mend0z0/Blender/Hardware/_Sub_HW_Blender/v1_20230918/Released Folder/v1.0 - 20230918/README.md

### This readme file explains the folder structure of this released version.

#### 1. Board Assembly: Any document that is related to assembly will be in this folder

	1. Assembly Guide:
		1. _MASM_Prj_vXY.html	--> This is for hand assembly
		2. _AASM_Prj_vXY.???	--> This is for machine assembly

	2. Board Statistics:
		1. _STATISTICS_Prj_vXY.txt

	3. BOM:
		1. _BOM_Prj_vXY.csv

	4. Netlist:
		1. _NETLIST_Prj_vXY.net

	5. Pick And Place:
		1. _PNP_Prj_vXY.csv

#### 2. Media Content: Any document that is related to assembly will be in this folder
	
	1. Picutre
		1. _3DView_Prj_vXY.png
		2. _3DView_Bottom_Prj_vXY.png
		3. _3DView_Top_Prj_vXY.png
		4. _CADView_Prj_vXY.png

	2. Video
		1. _Video_Prj_vXY_Title.mp4

#### 3. PCB Manufacturing: Any document that is related to manufacturing the board will be in this folder

	1. CNC Drill:
		_DRL_Prj_vXY.drl		
		_DRL_MAP_Prj_vXY.gbr

	2. Gerber:
		1. _GBR_Top_SilkScreen_Prj_vXY.gto
		2. _GBR_Top_Mask_Prj_vXY.gts
		3. _GBR_Top_Cu_Prj_vXY.gtl
		4. _GBR_In1_Cu_Prj_vXY.g2
		5. _GBR_In2_Cu_Prj_vXY.g3
		6. _GBR_In3_Cu_Prj_vXY.g4
		7. _GBR_In4_Cu_Prj_vXY.g5
		8. _GBR_Bottom_Cu_Prj_vXY.gbl
		9. _GBR_Bottom_Mask_Prj_vXY.gbs
		10. _GBR_Bottom_SilkScreen_Prj_vXY.gbo
		11. _GBR_EdgeCut_Prj_vXY.gml

	3. Stackup Information:
		_STACKUP_Prj_vXY.csv

	4. Stencil:
		_STC_Top_Prj_vXY.gtp
		_STC_Bottom_Prj_vXY.gbp
		_STC_EdgeCut_Prj_vXY.gml

#### 4. Schematic (PDF): Placing the PDF version of the schematic captures

#### 5. Source files: All the sources except the history files.

#### 6. STEP: The 3D Model file of the project will be in this folder.
	1. _STEP_Prj_vXY.stp
