mend0z0/Blender/Firmware/v1_20231222/Design Folder/_FW_Blender/Drivers/Peripherals/_drv_peripherals.h

/****************************************************************************************************
*
*   Project Name:       Blender
*   @Brief Description: Blending audio spec with light spectrum
*   File Status:	    DRAFT   (DRAFT , PRELIMINARY, CHECKED, RELEASED)
*
*	File Name:	xxxx.h
*	Version:	01
*	Revision:	01
*	Date:		2023/01/dd
*	License:	Open-source
*	******************************** Project Description *******************************************
*	@Detailed Description: The Blender project's purpose is to extract digitalized sound characteristics
*   like amplitude and frequency, which are transferring through the S/PDIF protocol, and display the amplitude
*   of different frequencies by the dominant color of the input VGA received signal. So the base color will be
*   determined by VGA input, and a spectrum of that color will be displayed over/on the DMX/WS2812 chip. Also,
*   the specification of the sound will be displayed on an OLED, and the sound will be played by a chip that has
*   an integrated DAC in it. The data to DAC will be transferred via the I2S protocol.
*
*	******************************** File Description *******************************************
*	@Detailed Description:
*
*
*
*	*********************************  Hardware Info  **********************************************
*   Name:       _HW_Blender
*   Version:    v1.0
*	*********************************  Processor Info **********************************************
*	Processor:          STM32F446RCT6 32-Bits
*	Clock Frequency:    180.000	MHz
*	RAM/SRAM Size:      128.00	KBytes
*	Flash Size:         256.00	KBytes
*	***********************************  Case Style  ***********************************************
*	Local Variables = camelCase			Global Variables = g_camelCase
*	Headers = SCREAMIN_SNAKE_CASE
*   Macros = SCREAMING_SNAKE_CASE
*   Const Variables = SCREAMING_SNAKE_CASE
*	Functions = PascalCase				Initialize Functions = _lower_case
*	Struct = lower_case					Struct.members = camelCase
*	Enum = lower_case					Enum Members = SNAKE_CASE
*	Pointer Variables = p_camelCase
*	*********************************** Contact Info ***********************************************
*	Author: Siavash Taher Parvar
*	Github: www.github.com/Mend0z0
****************************************************************************************************/
#ifndef _DRV_PERIPHERALS_H_
#define _DRV_PERIPHERALS_H_
/****************************************************************************************************
****************************       HEADERS DECLARATION       ****************************************
*****************************************************************************************************/
#include "main.h"

/****************************************************************************************************
****************************        MACRO DECLARATION         ***************************************
*****************************************************************************************************/

/****************************************************************************************************
****************************   DEFINED VARIABLES DECLARATION    *************************************
*****************************************************************************************************/
#define	PAM8003_DEFAULT_VALUE_PIN_SHDN  0U
#define PAM8003_DEFAULT_VALUE_PIN_VOL	0U

#define PCM1754_DEFAULT_VALUE_PIN_DMP	0U 		// (1 -> DMP ON, 0 -> DMP OFF)
#define PCM1754_DEFAULT_VALUE_PIN_FMT	1U		// (1 -> 16-bit right-justified, 0 -> 24-bit I2S format)
#define PCM1754_DEFAULT_VALUE_PIN_MUTE	1U		// (1 -> MUTE ON, 0 -> MUTE OFF)

#define SSD1306_DEFAULT_VALUE_PIN_RES	0U		//
#define SSD1306_DEFAULT_VALUE_PIN_DC	0U		//
#define PWR_EN_DEFAULT_VALUE_PIN		0U		//
#define LED_IND_DEFAULT_VALUE_PIN 		0U		//

#define	DMA2_SPI1_TX_EN					1U		//
#define	DMA1_FMPI2C1_TX_EN				2U		//
#define	DMA2_UART1_TX_EN				3U		//

#define	DMA2_SPI1_TX_DIS				4U		//
#define	DMA1_FMPI2C1_TX_DIS				5U		//
#define	DMA2_UART1_TX_DIS				6U		//

#define FMPI2C_ERROR_NACK				-2		//
#define	FMPI2C_ERROR_UNKNOWN			-3		//



/****************************************************************************************************
**************************     GLOBAL FUNCTIONS DECLARATION      ************************************
*****************************************************************************************************/

/****************************************************************************************************
*   @Brief Description:	This functions holds all the functions that will initialize all the peripherals registers.
*   Function Status: 	PRILIMINARY   (DRAFT , PRILIMINARY, CHECKED, RELEASED)
*
*	************************************************************************************************
*	Function Name:			_init_Peripherals()
*	Function Scope:			Global
*	Function Parameters:	void
*	Function Return Type:	void
*	************************************************************************************************/
void _init_Peripherals( void );

/*			Digital-to-analog converter							*/

/****************************************************************************************************
*   @Brief Description:	Updating the DAC output value based on percents not real output voltage.
*   Function Status: 	PRILIMINARY   (DRAFT , PRILIMINARY, CHECKED, RELEASED)
*
*	************************************************************************************************
*	Function Name:			DACUpdate()
*	Function Scope:			Global
*	Function Parameters:	uint8_t dacValue (It's a percent from 0% to 100%)
*	Function Return Type:	void
*	************************************************************************************************/
void DACUpdate( uint8_t dacValue);

/*			General-purpose timers (TIM3)						*/

/****************************************************************************************************
*   @Brief Description:	Preset the TIM3 counter register and enabling the timer
*   Function Status: 	PRILIMINARY   (DRAFT , PRILIMINARY, CHECKED, RELEASED)
*
*	************************************************************************************************
*	Function Name:			TIM3Enable()
*	Function Scope:			Global
*	Function Parameters:	void
*	Function Return Type:	void
*	************************************************************************************************/
void TIM3Enable( void );

/****************************************************************************************************
*   @Brief Description: Disable Timer3
*   Function Status: 	PRILIMINARY   (DRAFT , PRILIMINARY, CHECKED, RELEASED)
*
*	************************************************************************************************
*	Function Name:			TIM3Disable()
*	Function Scope:			Global
*	Function Parameters:	void
*	Function Return Type:	void
*	************************************************************************************************/
void TIM3Disable( void );

/****************************************************************************************************
*   @Brief Description:	Update CCR3 register of Timer 3
*   Function Status: 	PRILIMINARY   (DRAFT , PRILIMINARY, CHECKED, RELEASED)
*
*	************************************************************************************************
*	Function Name:			TIM3UpdateCCR3()
*	Function Scope:			Global
*	Function Parameters:	uint32_t ccrValue
*	Function Return Type:	void
*	************************************************************************************************/
bool TIM3UpdateCCR3( void );

/*			Inter-integrated circuit (I2C) interface			*/

/****************************************************************************************************
*   @Brief Description:	Sending an array of data over FMPI2C1
*   Function Status: 	PRILIMINARY   (DRAFT , PRILIMINARY, CHECKED, RELEASED)
*
*	************************************************************************************************
*	Function Name:			FMPI2C1DataTx()
*	Function Scope:			Global
*	Function Parameters:	uint8_t slaveAddr, uint8_t *data, uint32_t buffSize
*	Function Return Type:	int32_t
*	************************************************************************************************/
int32_t FMPI2C1DataTx( uint8_t slaveAddr, uint8_t *data, uint32_t buffSize);

/*			Universal asynchronous receiver transmitter			*/

/****************************************************************************************************
*   @Brief Description: Sending out an array of data over UART
*   Function Status: 	PRILIMINARY   (DRAFT , PRILIMINARY, CHECKED, RELEASED)
*
*	************************************************************************************************
*	Function Name:			UART1DataTx()
*	Function Scope:			Global
*	Function Parameters:	uint8_t *data, uint32_t buffSize
*	Function Return Type:	int32_t
*	************************************************************************************************/
int32_t UART1DataTx( uint8_t *data, uint32_t buffSize);

/*			Inter-IC sound										*/
int8_t I2SDataTx( uint32_t *data);



#endif /* _DRV_PERIPHERALS_H_  */

/****************************************************************************************************
*	Revision History (Description (author, date: yyyy/mm/dd))
*
****************************************************************************************************/

/************************************     END OF THE FILE      *************************************/
