mend0z0/Blender/Firmware/v1_20231222/Design Folder/_FW_Blender/Core/Src/ISR.c

/****************************************************************************************************
*
*   	Project Name:       Blender
*   	@Brief Description: Blending audio spec with light spectrum
*   	File Status:	    PRELIMINARY   (DRAFT , PRELIMINARY, CHECKED, RELEASED)
*
*	File Name:	isr.c
*	Version:	01
*	Revision:	01
*	Date:		2024/02/19
*	License:	Open-source
********************************* Project Description *******************************************
*		@Detailed Description: The Blender project's purpose is to extract digitalized sound characteristics
*   	like amplitude and frequency, which are transferring through the S/PDIF protocol, and display the amplitude
*   	of different frequencies by the dominant color of the input VGA received signal. So the base color will be
*   	determined by VGA input, and a spectrum of that color will be displayed over/on the DMX/WS2812 chip. Also,
*   	the specification of the sound will be displayed on an OLED, and the sound will be played by a chip that has
*   	an integrated DAC in it. The data to DAC will be transferred via the I2S protocol.
*
********************************* File Description *******************************************
*	@Detailed Description:
*
*
**********************************  Hardware Info  **********************************************
*   	Name:       _HW_Blender
*   	Version:    v1.0
**********************************  Processor Info **********************************************
*	Processor:          STM32F446RCT6 32-Bits
*	Clock Frequency:    180.000	MHz
*	RAM/SRAM Size:      128.00	KBytes
*	Flash Size:         256.00	KBytes
************************************  Case Style  ***********************************************
*	Local Variables = camelCase			Global Variables = g_camelCase
*	Headers = SCREAMIN_SNAKE_CASE
*   	Macros = SCREAMING_SNAKE_CASE
*   	Const Variables = SCREAMING_SNAKE_CASE
*	Functions = PascalCase				Initialize Functions = _lower_case
*	Struct = lower_case				Struct.members = camelCase
*	Enum = lower_case				Enum Members = SNAKE_CASE
*	Pointer Variables = p_camelCase
************************************ Contact Info ***********************************************
*	Author:	Siavash Taher Parvar
*	Github: github.com/Mend0z0
****************************************************************************************************/

/****************************************************************************************************
****************************       HEADERS DECLARATION       ****************************************
*****************************************************************************************************/
#include "isr.h"

/****************************************************************************************************
****************************   CONST VARIABLES DECLARATION    ***************************************
*****************************************************************************************************/

/****************************************************************************************************
****************************   GLOB. VARIABLES DECLARATION    ***************************************
*****************************************************************************************************/
extern SemaphoreHandle_t xBinarySemaphoreDMA1Stream5;		//
extern SemaphoreHandle_t xBinarySemaphoreTIM3;			// The semaphore has been created in this .c file so it's the original variable.
extern SemaphoreHandle_t xBinarySemaphoreFMPI2C;		//
extern SemaphoreHandle_t xBinarySemaphoreUSART1;		//

extern __IO uint8_t ws2812ColorBits[WS2812_NO_COLOR_BITS];
extern __IO uint8_t ws2812ColorBitIndexCnt;

/****************************************************************************************************
***********************     STATIC/LOCAL FUNCTIONS DECLARATION      *********************************
*****************************************************************************************************/

/****************************************************************************************************
****************************         GLOBAL FUNTIONS         ****************************************
*****************************************************************************************************/

/****************************************************************************************************
****************************         STATIC FUNTIONS         ****************************************
*****************************************************************************************************/


/*			SysTick Timer	 									*/

/****************************************************************************************************
*   @Brief Description: SysTick handler implementation that also clears overflow flag.
*   Function Status: 	PRELIMINARY   (DRAFT , PRELIMINARY, CHECKED, RELEASED)
*
*************************************************************************************************
*	Function Name:		SysTick_Handler()
*	Function Scope:         Local(static)
*	Function Parameters:	void
*	Function Return Type:	void
*************************************************************************************************
*	@Detailed Description: (Do numbering and tag the number to each part of code)
*	(1)
*	(2)
*************************************************************************************************
*	Revision History (Description (author, date: yyyy/mm/dd))
*
****************************************************************************************************/
#if (USE_CUSTOM_SYSTICK_HANDLER_IMPLEMENTATION == 0)
  void SysTick_Handler (void)
  {
    /* Clear overflow flag */
    SysTick->CTRL;

    if (xTaskGetSchedulerState() != taskSCHEDULER_NOT_STARTED) {
	/* Call tick handler */
	xPortSysTickHandler();
    }
  }
#endif

/*			Power controller 									*/


/*			Reset and clock control 							*/


/*			General-purpose I/Os								*/


/*			Direct memory access controller						*/
void DMA1_Stream0_IRQHandler( void )
{

}

void DMA1_Stream1_IRQHandler( void )
{

}

void DMA1_Stream2_IRQHandler( void )
{

}

void DMA1_Stream3_IRQHandler( void )
{

}

void DMA1_Stream4_IRQHandler( void )
{

}

/****************************************************************************************************
*   @Brief Description:	DMA1 Stream5 Interrupt handler
*   Function Status: 	PRELIMINARY   (DRAFT , PRELIMINARY, CHECKED, RELEASED)
*
*************************************************************************************************
*	Function Name:		DMA1_Stream5_IRQHandler()
*	Function Scope:         Local(static)
*	Function Parameters:	void
*	Function Return Type:	void
*************************************************************************************************
*	@Detailed Description: (Do numbering and tag the number to each part of code)
*	(1) Disable Transfer complete interrupt.
*	(2) Upon completion sending the stop for releasing the line.
*	(3) This will give back the semaphore so we'll back to continue FMPI2CDataTx
*************************************************************************************************
*	Revision History (Description (author, date: yyyy/mm/dd))
*
****************************************************************************************************/
void DMA1_Stream5_IRQHandler( void )
{
  BaseType_t xHigherPriorityTaskWoken = pdFALSE;

  DMA1_Stream5->CR &= ~DMA_SxCR_TCIE;				// (1)
  FMPI2C1->CR2 |= FMPI2C_CR2_STOP;				// (2)
  xSemaphoreGiveFromISR( xBinarySemaphoreDMA1Stream5, &xHigherPriorityTaskWoken);	// (3)

  /* Yield if xHigherPriorityTaskWoken is true.  The actual macro used here is port specific. */
  portYIELD_FROM_ISR( xHigherPriorityTaskWoken );
}

void DMA1_Stream6_IRQHandler( void )
{

}

void DMA2_Stream0_IRQHandler( void )
{

}

void DMA2_Stream1_IRQHandler( void )
{

}

void DMA2_Stream2_IRQHandler( void )
{

}

void DMA2_Stream3_IRQHandler( void )
{

}

void DMA2_Stream4_IRQHandler( void )
{

}

void DMA2_Stream5_IRQHandler( void )
{

}

/****************************************************************************************************
*   @Brief Description: DMA2 Stream6 interrupt handler
*   Function Status: 	PRELIMINARY   (DRAFT , PRELIMINARY, CHECKED, RELEASED)
*
*	************************************************************************************************
*	Function Name:			DMA2_Stream6_IRQHandler()
*	Function Scope:         Local(static)
*	Function Parameters:	void
*	Function Return Type:	void
*	************************************************************************************************
*	@Detailed Description: (Do numbering and tag the number to each part of code)
*	(1) Clearing the flag by writing a one.
*	(2) Disable Transfer complete interrupt.
*	************************************************************************************************
*	Revision History (Description (author, date: yyyy/mm/dd))
*
****************************************************************************************************/
void DMA2_Stream6_IRQHandler( void )
{
  DMA2->HIFCR |= DMA_HIFCR_CTCIF7;	// (1)
  DMA2_Stream7->CR &= ~DMA_SxCR_TCIE;	// (2)
}

/*			Analog-to-digital converter	1						*/


/*			Analog-to-digital converter	2						*/


/*			Analog-to-digital converter	3						*/


/*			Digital-to-analog converter							*/


/*			Advanced-control timers (TIM1)						*/
void TIM1_IRQHandler( void )
{

}

/*			General-purpose timers (TIMER2)						*/


/*			General-purpose timers (TIMER3)						*/

/****************************************************************************************************
*   @Brief Description:	TIM3 Interrupt handler
*   Function Status: 	PRELIMINARY   (DRAFT , PRELIMINARY, CHECKED, RELEASED)
*
*	************************************************************************************************
*	Function Name:			TIM3_IRQHandler()
*	Function Scope:         Local(static)
*	Function Parameters:	void
*	Function Return Type:	void
*	************************************************************************************************
*	@Detailed Description: (Do numbering and tag the number to each part of code)
*	(1) Clearing the overflow flag
*	(2) Giving back the semaphore
*	************************************************************************************************
*	Revision History (Description (author, date: yyyy/mm/dd))
*
****************************************************************************************************/
void TIM3_IRQHandler( void ){
  BaseType_t xHigherPriorityTaskWoken = pdFALSE;
  TIM3->SR &= ~TIM_SR_UIF;							// (1)
  TIM3->CCR3 = ws2812ColorBits[ws2812ColorBitIndexCnt];					// (1)
  ws2812ColorBitIndexCnt++;
  if(ws2812ColorBitIndexCnt == WS2812_NO_COLOR_BITS)
    {
      ws2812ColorBitIndexCnt = 0;
      xSemaphoreGiveFromISR( xBinarySemaphoreTIM3, &xHigherPriorityTaskWoken);	// (2)
      /* Yield if xHigherPriorityTaskWoken is true.  The actual macro used here is port specific. */
      portYIELD_FROM_ISR( xHigherPriorityTaskWoken );
    }
}

/*			Real-time clock										*/


/*			Inter-integrated circuit (I2C) interface			*/

/****************************************************************************************************
*   @Brief Description: FMPI2C1 Event interrupt handler.
*   Function Status: 	PRELIMINARY   (DRAFT , PRELIMINARY, CHECKED, RELEASED)
*
*************************************************************************************************
*	Function Name:			FMPI2C1_EV_IRQHandler()
*	Function Scope:         Local(static)
*	Function Parameters:	void
*	Function Return Type:	void
*************************************************************************************************
*	@Detailed Description: (Do numbering and tag the number to each part of code)
*	(1) Checking if the interrupt has been triggered from a NACK flag
*	(2) Disable the NACK interrupt for servicing it outside of ISR.
*	(3) This will give back the semaphore so we'll back to continue FMPI2CDataTx
*	(4) Checking if the interrupt has been triggered from a complete transfer flag (the slave address has been configured...)
*	(5) Enabling the DMA for transferring the data via DMA
*	(6) No more needed after confirming the slave address. So we disable TXIE.
*************************************************************************************************
*	Revision History (Description (author, date: yyyy/mm/dd))
*
****************************************************************************************************/
void FMPI2C1_EV_IRQHandler( void )
{
  BaseType_t xHigherPriorityTaskWoken = pdFALSE;

  if((FMPI2C1->ISR & FMPI2C_ISR_NACKF) == FMPI2C_ISR_NACKF)	// (1)
    {
      FMPI2C1->CR1 &= ~FMPI2C_CR1_NACKIE;			// (2)
      xSemaphoreGiveFromISR( xBinarySemaphoreFMPI2C, &xHigherPriorityTaskWoken);	// (3)
    }
  else if((FMPI2C1->ISR & FMPI2C_ISR_TXIS) == FMPI2C_ISR_TXIS)	// (4)
    {
      FMPI2C1->CR1 |= FMPI2C_CR1_TXDMAEN;			// (5)
      FMPI2C1->CR1 &= ~FMPI2C_CR1_TXIE;				// (6)
    }
  /* Yield if xHigherPriorityTaskWoken is true.  The actual macro used here is port specific. */
  portYIELD_FROM_ISR( xHigherPriorityTaskWoken );
}

void FMPI2C1_ER_IRQHandler( void )
{

}

/*			Universal asynchronous receiver transmitter			*/

/****************************************************************************************************
*   	@Brief Description: 	USART1 Interrupt handler
*   	Function Status: 	PRELIMINARY   (DRAFT , PRELIMINARY, CHECKED, RELEASED)
*
*************************************************************************************************
*	Function Name:		USART1_IRQHandler()
*	Function Scope:         Local(static)
*	Function Parameters:	void
*	Function Return Type:	void
*************************************************************************************************
*	@Detailed Description: (Do numbering and tag the number to each part of code)
*	(1) Disabling the USART interrupt
*	(2) Giving back the semaphore
*************************************************************************************************
*	Revision History (Description (author, date: yyyy/mm/dd))
*
****************************************************************************************************/
void USART1_IRQHandler( void )
{
  BaseType_t xHigherPriorityTaskWoken = pdFALSE;
  USART1->CR1 &= ~USART_CR1_TCIE;						// (1)
  xSemaphoreGiveFromISR( xBinarySemaphoreUSART1, &xHigherPriorityTaskWoken);	// (2)
  /* Yield if xHigherPriorityTaskWoken is true.  The actual macro used here is port specific. */
  portYIELD_FROM_ISR( xHigherPriorityTaskWoken );
}

/*			Inter-IC sound										*/


/*			SPDIF receiver interface							*/


/************************************     END OF THE FILE      *************************************/
